ytmytm/1551-rePico/experimental/firmware/include/lcd.h

// Ansteuerung eines HD44780 kompatiblen LCD im 4-Bit-Interfacemodus
// http://www.mikrocontroller.net/articles/AVR-GCC-Tutorial/LCD-Ansteuerung
//
// adoption for portexpander PCF8574 via I2C:
// implementation: F00K42
// last change: 11/10/2025

#ifndef LCD_ROUTINES_H
#define LCD_ROUTINES_H

#include "i2c.h"

////////////////////////////////////////////////////////////////////////////////
// Pinbelegung für das LCD

#define LCD_RS          (1<<0)      // (RS: 1=Data, 0=Command)
#define LCD_RW          (1<<1)
#define LCD_EN          (1<<2)      // (EN: 1-Impuls für Daten)
#define LCD_BACKLIGHT   (1<<3)

////////////////////////////////////////////////////////////////////////////////
// LCD Ausführungszeiten (MS=Millisekunden, US=Mikrosekunden)

#define LCD_BOOTUP_MS           50 	// 15
#define LCD_ENABLE_US           20	// 20
#define LCD_WRITEDATA_US        46	// 46
#define LCD_COMMAND_US          42	// 42

#define LCD_SOFT_RESET_MS1      5	// 5
#define LCD_SOFT_RESET_MS2      1	// 1
#define LCD_SOFT_RESET_MS3      1	// 1
#define LCD_SET_4BITMODE_MS     5	// 5

#define LCD_CLEAR_DISPLAY_MS    2	// 2
#define LCD_CURSOR_HOME_MS      2	// 2

////////////////////////////////////////////////////////////////////////////////
// Zeilendefinitionen des verwendeten LCD

// LCD 16x4
#define LCD_COLS (16)
#define LCD_ROWS (4)

// LCD 20x4
// #define LCD_COLS (20)
// #define LCD_ROWS (4)

////////////////////////////////////////////////////////////////////////////////

#ifndef _EXTERN_
#define _EXTERN_ extern
#endif

// function pointer to be used later
_EXTERN_ void (*lcd_out)(uint8_t);

void pcf_lcd_out( uint8_t data );

void error_lcd_out( uint8_t data );
////////////////////////////////////////////////////////////////////////////////
// Initialisierung: muss ganz am Anfang des Programms aufgerufen werden.
void lcd_setup( void );

////////////////////////////////////////////////////////////////////////////////
// LCD löschen
void lcd_clear( void );

////////////////////////////////////////////////////////////////////////////////
// Cursor in die 1. Zeile, 0-te Spalte
void lcd_home( void );

////////////////////////////////////////////////////////////////////////////////
// Cursor an eine beliebige Position 
void lcd_setcursor( const uint8_t spalte, const uint8_t zeile );

////////////////////////////////////////////////////////////////////////////////
// Ausgabe eines einzelnen Zeichens an der aktuellen Cursorposition 
void lcd_data( const uint8_t data );

////////////////////////////////////////////////////////////////////////////////
// Ausgabe eines Strings an der aktuellen Cursorposition 
void lcd_string( const char *data );

////////////////////////////////////////////////////////////////////////////////
// Schreibt einen String auf das LCD mit erweiterten Parametern
// start:   Position des erstes Zeichens im String was ausgegeben werden soll
// length:  Maximale Anzahl der Zeichen die Ausgegeben werden sollen
void lcd_print( const char *string, const uint8_t start, const uint8_t length);

////////////////////////////////////////////////////////////////////////////////
// Definition eines benutzerdefinierten Sonderzeichens.
// data muss auf ein Array[8] mit den Zeilencodes des zu definierenden Zeichens
// zeigen
void lcd_generatechar( const uint8_t code, const uint8_t *data );

////////////////////////////////////////////////////////////////////////////////
// Ausgabe eines Kommandos an das LCD.
void lcd_command( const uint8_t data );

////////////////////////////////////////////////////////////////////////////////
// set "bright" mode or "light" mode for 128x64 display
void lcd_setbright( bool bright_on );

////////////////////////////////////////////////////////////////////////////////
// LCD Befehle und Argumente.
// Zur Verwendung in lcd_command

// Clear Display -------------- 0b00000001
#define LCD_CLEAR_DISPLAY       (1<<0)

// Cursor Home ---------------- 0b0000001x
#define LCD_CURSOR_HOME         (1<<1)

// Set Entry Mode ------------- 0b000001xx
#define LCD_SET_ENTRY           (1<<2)

#define LCD_ENTRY_DECREASE      0x00
#define LCD_ENTRY_INCREASE      0x02
#define LCD_ENTRY_NOSHIFT       0x00
#define LCD_ENTRY_SHIFT         0x01

// Set Display ---------------- 0b00001xxx
#define LCD_SET_DISPLAY         (1<<3)

#define LCD_DISPLAY_OFF         0x00
#define LCD_DISPLAY_ON          0x04
#define LCD_CURSOR_OFF          0x00
#define LCD_CURSOR_ON           0x02
#define LCD_BLINKING_OFF        0x00
#define LCD_BLINKING_ON         0x01

// Set Shift ------------------ 0b0001xxxx
#define LCD_SET_SHIFT           (1<<4)

#define LCD_CURSOR_MOVE         0x00
#define LCD_DISPLAY_SHIFT       0x08
#define LCD_SHIFT_LEFT          0x00
#define LCD_SHIFT_RIGHT         0x04

// Set Function --------------- 0b001xxxxx
#define LCD_SET_FUNCTION        (1<<5)

#define LCD_FUNCTION_4BIT       0x00
#define LCD_FUNCTION_8BIT       0x10
#define LCD_FUNCTION_1LINE      0x00
#define LCD_FUNCTION_2LINE      0x08
#define LCD_FUNCTION_5X7        0x00
#define LCD_FUNCTION_5X10       0x04

#define LCD_SOFT_RESET          0x30

// Set CG RAM Address --------- 0b01xxxxxx  (Character Generator RAM)
#define LCD_SET_CGADR           (1<<6)

// Set DD RAM Address --------- 0b1xxxxxxx  (Display Data RAM)
#define LCD_SET_DDADR           (1<<7)

#endif
