ytmytm/1551-rePico/experimental/firmware/include/gcr.h

/**********************************
 * GCR Routines header
 *
 * Author: F00K42
 * Last change: 2021/12/31
***********************************/

#ifndef _GCR_HEADER_
#define _GCR_HEADER_

#include <stdint.h>

void ConvertToGCR(const uint8_t *source_buffer, uint8_t *destination_buffer);
void ConvertFromGCR(const uint8_t *source_buffer, uint8_t *destination_buffer);

#endif // _GCR_HEADER_
